rohith-scandron/SHAKE_FOB_REV-A/band6_watchfaces/cat_blink/preview.gif

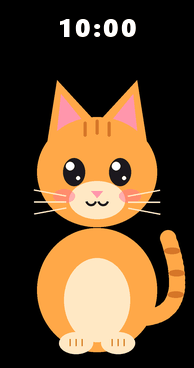
band6_watchfaces/cat_blink/preview.gif
