rohith-scandron/SHAKE_FOB_REV-A/band6_watchfaces/scubacat/preview.gif

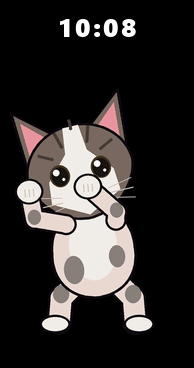
band6_watchfaces/scubacat/preview.gif
