rohith-scandron/SHAKE_FOB_REV-A/band6_watchfaces/speed400/preview.gif

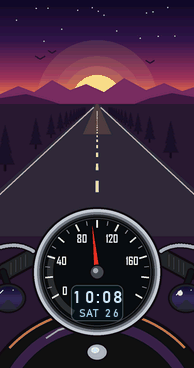
band6_watchfaces/speed400/preview.gif
