rohith-scandron/SHAKE_FOB_REV-A/band6_watchfaces/spidey/preview_fast.gif

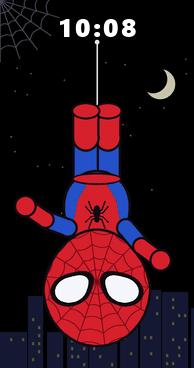
band6_watchfaces/spidey/preview_fast.gif
