rohith-scandron/SHAKE_FOB_REV-A/datasheets/johanson_page3.png

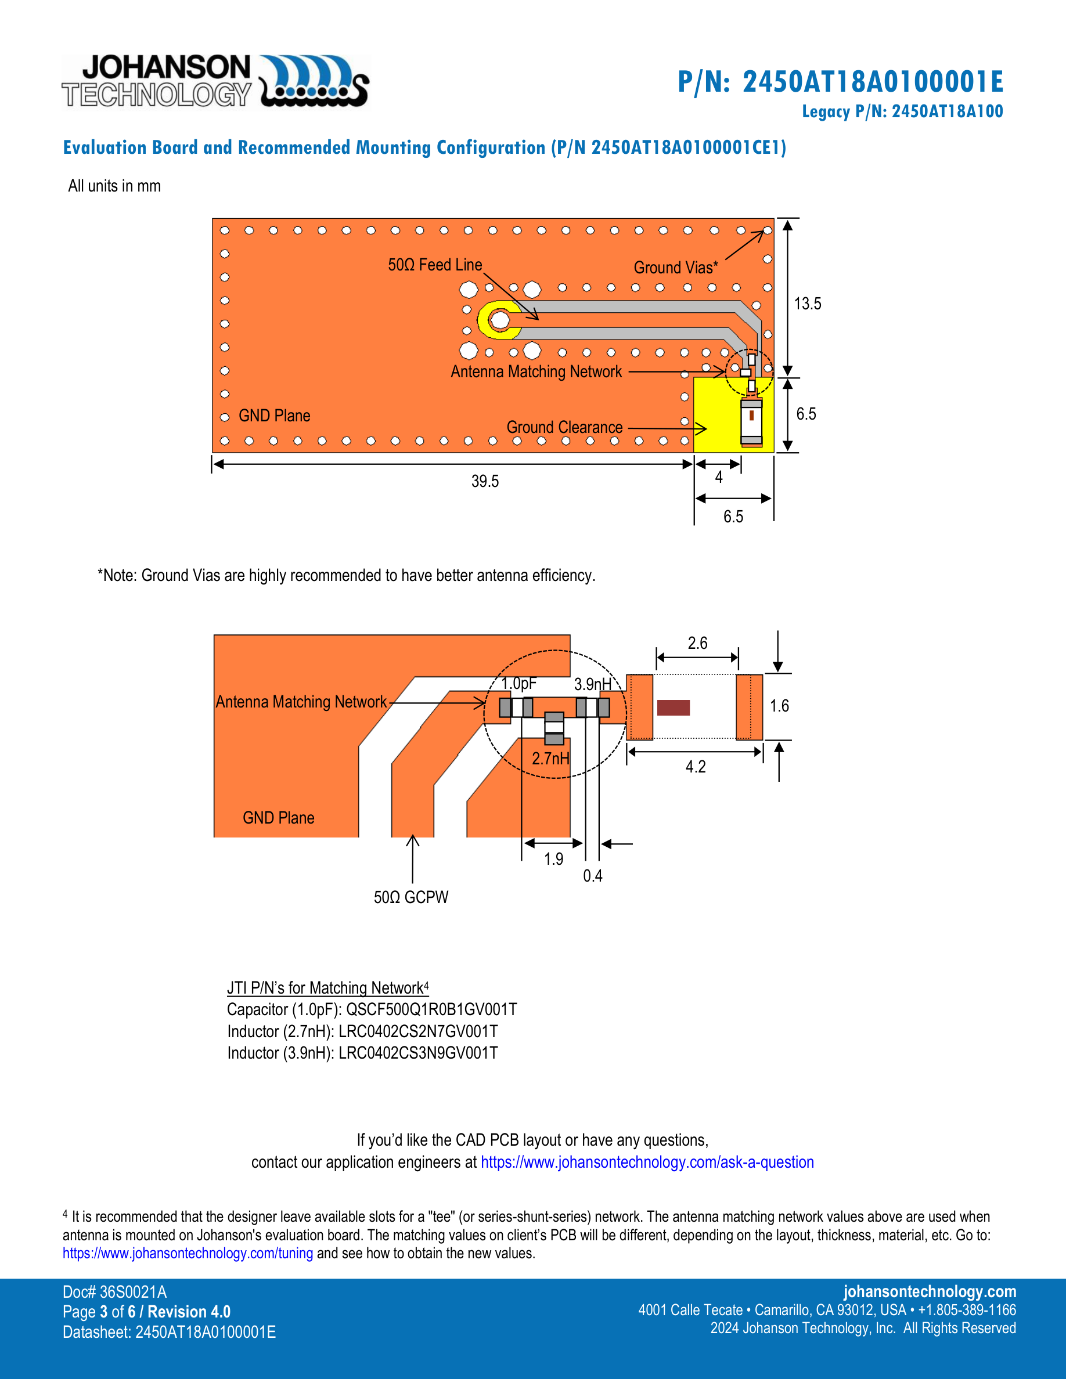
datasheets/johanson_page3.png
