rohith-scandron/SHAKE_FOB_REV-A/keychain_case/preview.png

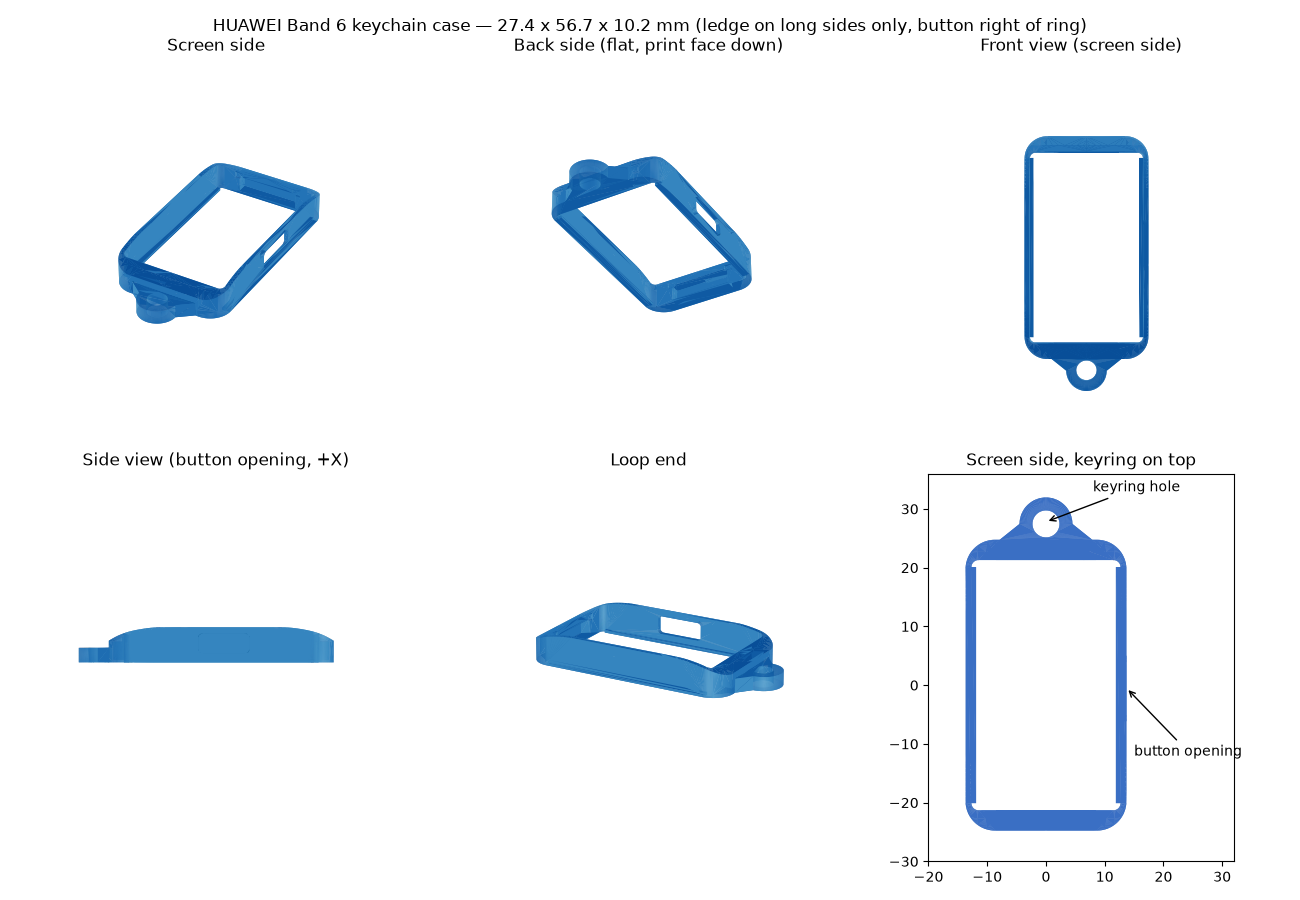
keychain_case/preview.png
